Eraikizpi/Eraikizpi-V2/STLs/Z_end_stop.STL

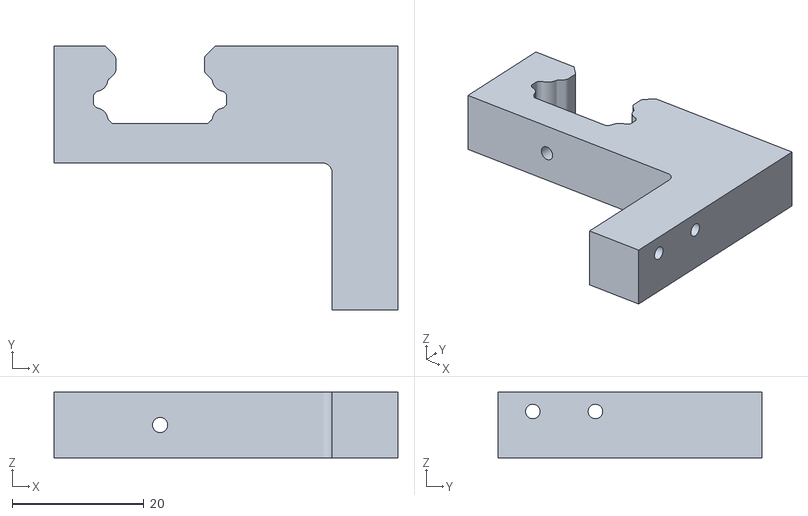
[picture p15: CAD file, 2015-03-11]
STLs/Z_end_stop.STL
52.2 x 40.0 x 10.0
