Eraikizpi/Eraikizpi-V2/STLs/BP_flex_joint.STL

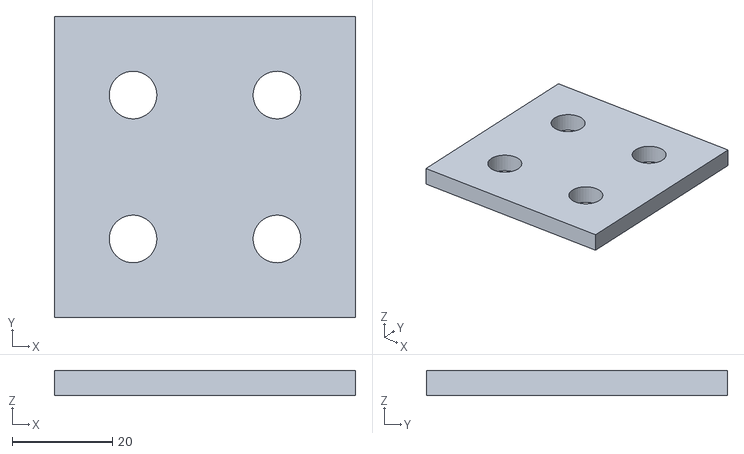
[picture p16: CAD file, 2015-03-11]
STLs/BP_flex_joint.STL
60.0 x 60.0 x 5.00
