Eraikizpi/Eraikizpi-V2/STLs/shooter_1.STL

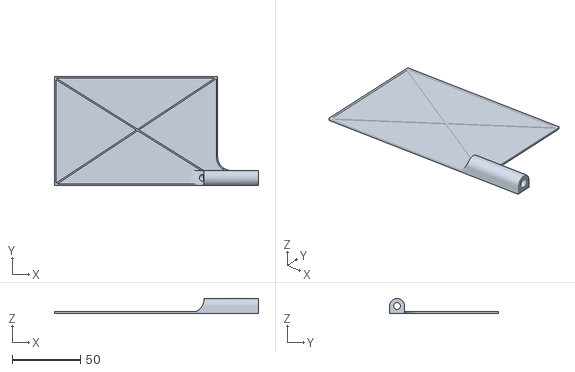
[picture p17: CAD file, 2015-03-11]
STLs/shooter_1.STL
150.0 x 80.0 x 11.0
