Eraikizpi/Eraikizpi-V2/STLs/Tank_base_stop.STL

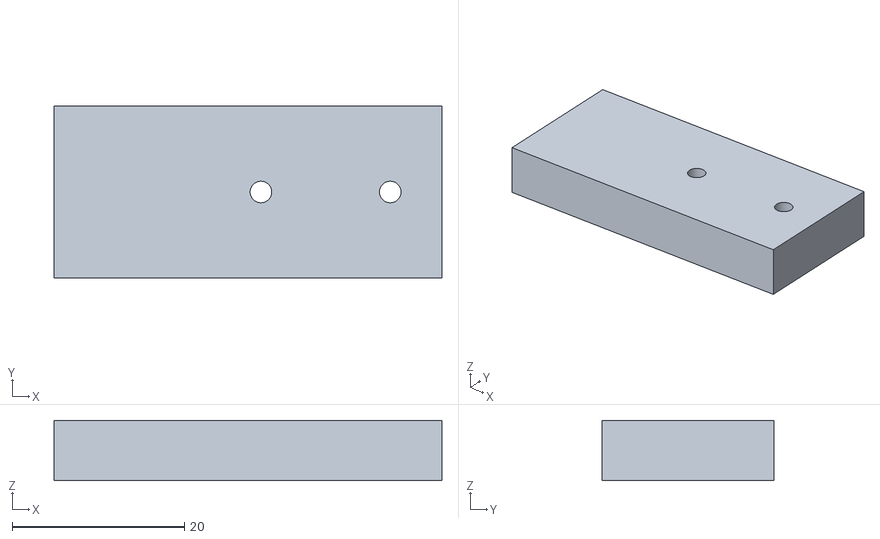
[picture p18: CAD file, 2015-03-11]
STLs/Tank_base_stop.STL
45.0 x 20.0 x 7.00
