Eraikizpi/Eraikizpi-V2/STLs/Bisagra.STL

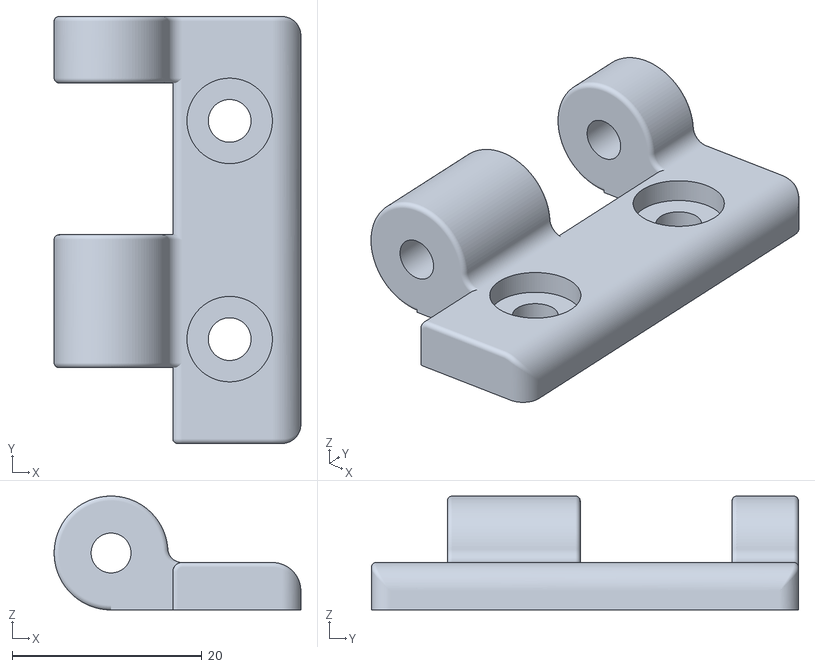
[picture p19: CAD file, 2015-03-11]
STLs/Bisagra.STL
26.0 x 45.0 x 12.0
