Eraikizpi/Eraikizpi-V2/STLs/Z_LM8UU_base.STL

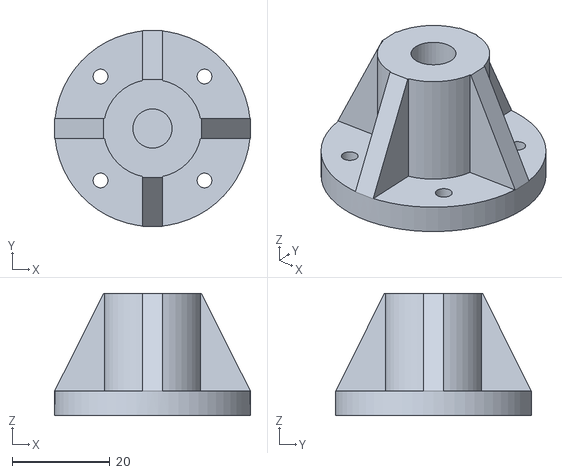
[picture p20: CAD file, 2015-03-11]
STLs/Z_LM8UU_base.STL
40.0 x 40.0 x 25.0
