Eraikizpi/Eraikizpi-V2/STLs/shooter_22.STL

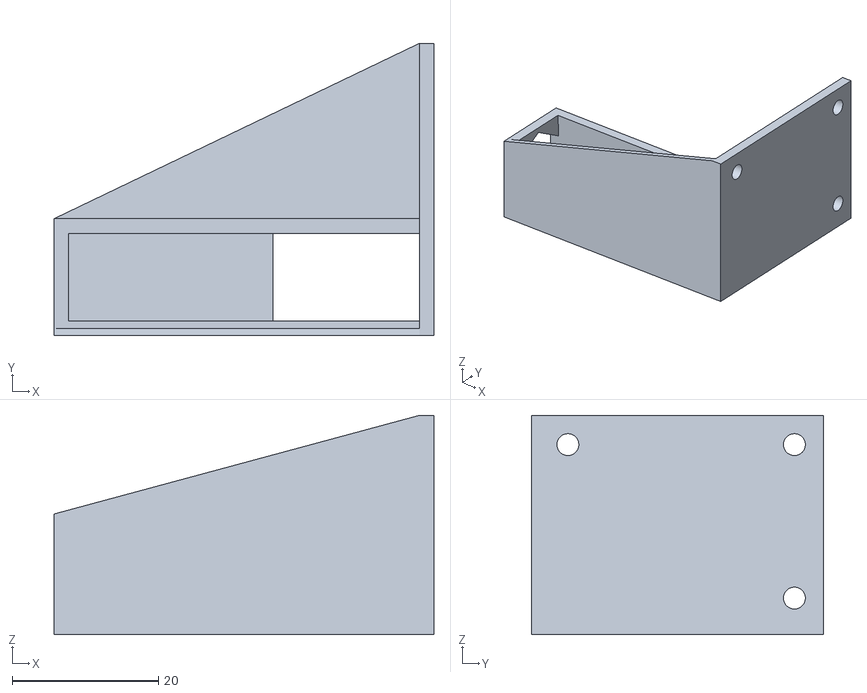
[picture p21: CAD file, 2015-03-11]
STLs/shooter_22.STL
52.0 x 40.0 x 30.0
