Eraikizpi/Eraikizpi-V2/STLs/passive_tilt_stopper.STL

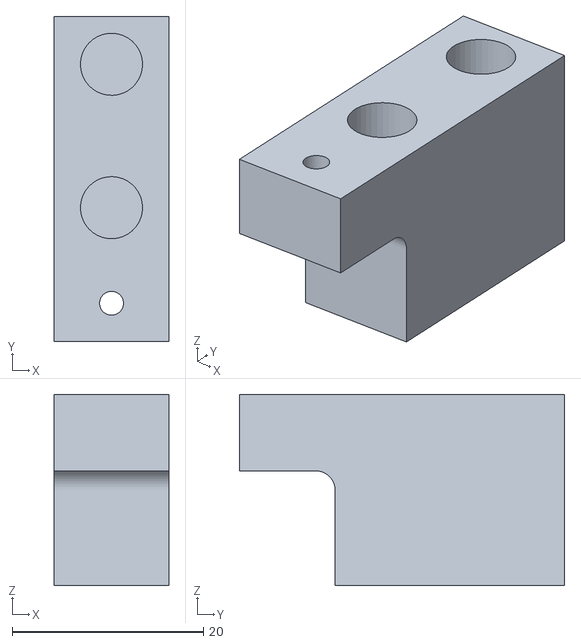
[picture p22: CAD file, 2015-03-11]
STLs/passive_tilt_stopper.STL
12.0 x 34.0 x 20.0
